cliffanet/sky-meter/cube/source/jump/proc.cpp

#include "proc.h"
#include "bmp280.h"
#include "altcalc.h"
#include "logbook.h"
#include "saver.h"
#include "bargraph.h"
#include "../sys/trwire.h"
#include "../sys/stm32drv.h"
#include "../sys/maincfg.h"
#include "../sys/power.h"
#include "../sys/err.h"
#include "../sys/log.h"
#include "../view/page.h"

#include <cmath>
#include "string.h"

#if HWVER < 2
static TransSPI _spi(GPIOB, GPIO_PIN_0);
#else
static TransSPI _spi(GPIOB, GPIO_PIN_10);
#endif
static BMP280 _bmp(_spi);
static float _press = 0, _temp = 0;

static AltCalc _ac;
static AltJmp _jmp(false);

#ifdef USE_JMPINFO
static AltSqBig _sq;
static AltStrict _jstr;
#endif // USE_JMPINFO

static LogBook::item_t _last = { 0 };

static uint8_t page = 0;

#ifdef USE_JMPTRACE
static jmp::log_ring_t _log;
static int _lmin = 0, _lmax = 0;
#endif // USE_JMPTRACE

    //-----------------------------------
    //---           draw
    //-----------------------------------

    static int16_t alt() {
        // Для отображения высоты app() лучше подходит,
        // т.к. она точнее показывает текущую высоту,
        // опаздывает от неё меньше, чем avg()
        int16_t alt = round(_ac.app().alt());
        int16_t o = alt % ALT_STEP;
        alt -= o;
        if (abs(o) > ALT_STEP_ROUND) alt+= o >= 0 ? ALT_STEP : -ALT_STEP;
        return alt;
    }

    static const char *strtm(char *s, uint32_t tm) {
        tm /= 1000;
        int sec = tm % 60;
        tm -= sec;

        if (tm <= 0) {
            sprn("%d s", sec);
            return s;
        }

        tm /= 60;
        int min = tm % 60;
        tm -= min;

        if (tm <= 0) {
            sprn("%d:%02d", min, sec);
            return s;
        }

        sprn("%ld:%02d:%02d", tm/60, min, sec);
        return s;
    }

    static const char *modestr(char *s, AltJmp::mode_t m) {
        const char *pstr =
            m == AltJmp::INIT       ? "INIT" :
            m == AltJmp::GROUND     ? "GND" :
            m == AltJmp::TAKEOFF    ? "TOFF" :
            m == AltJmp::FREEFALL   ? "FF" :
            m == AltJmp::CANOPY     ? "CNP" : "-";
        strcpy(s, pstr);
        return s;
    }

    //-----------------------------------
    static void _draw(DSPL_ARG) {
        Dspl::drawBatt(u8g2);
        Dspl::drawClock(u8g2);
        Dspl::drawServ(u8g2);
        
        char s[strsz], m[strsz], t[strsz];

        err::tostr(s, strsz);
        if (s[0] != '\0') {
            DSPL_FONT(u8g2_font_helvB08_tr);
            DSPL_STR(0, 17, s);
        }

    if (!_ac.isempty()) {
        // info
        DSPL_FONT(u8g2_font_6x13B_tr);

        uint8_t y = 40;
        sprn("%.1f m/s", _ac.avg().speed());
        DSPL_STR(static_cast<int>(DSPL_S_RIGHT(s))+60-DSPL_DWIDTH, y, s);

        y += DSPL_S_HEIGHT+2;
        sprn("%s (%s)", modestr(m, _jmp.mode()), strtm(t, _jmp.tm()));
        DSPL_STR(0, y, s);

#ifdef USE_JMPINFO
        y += DSPL_S_HEIGHT+2;
        if (_jmp.newtm() > 0) {
            sprn("new: %s (%ld)", strtm(t, _jmp.newtm()), _jmp.newcnt());
            DSPL_STR(0, y, s);
        }

        y += DSPL_S_HEIGHT+2;
        if (_jmp.ff().active()) {
            sprn("ff: %d", _jmp.ff().num());
            DSPL_STR(0, y, s);
        }

        y += DSPL_S_HEIGHT+2;
        sprn("q:%0.1f(%s)", _sq.val(), strtm(t, _sq.tm()));
        DSPL_STR(0, y, s);

        y += DSPL_S_HEIGHT+2;
        sprn("p[%0.0f]:%0.1f", _ac.pressgnd(), _press-_ac.pressgnd());
        DSPL_STR(0, y, s);

        //sprn("s[%d]:%s(%s)", _jstr.prof().num(), modestr(m, _jstr.mode()), strtm(t, _jstr.tm()));
        sprn("t:%.2f", _temp);
        DSPL_STR(DSPL_S_RIGHT(s)-15, DSPL_DHEIGHT-1, s);
#endif // USE_JMPINFO

    }

        // alt
        if (_ac.isempty())
            sprn("-");
        else
            sprn("%d", alt());
        
        switch (page) {
            case 0: {
                // alt
                DSPL_FONT(u8g2_font_logisoso62_tn);
                DSPL_STR(DSPL_S_RIGHT(s), 80, s);
            }
            break;
#ifdef USE_JMPTRACE
            case 1: {
                // alt
                DSPL_FONT(u8g2_font_fub20_tr);

                int y = DSPL_S_HEIGHT + 20;
                DSPL_STR(130-DSPL_S_WIDTH(s), y, s);

                // вертикальная шкала
                DSPL_LINE(DSPL_DWIDTH-5, 0,                 DSPL_DWIDTH, 0);
                DSPL_LINE(DSPL_DWIDTH-5, DSPL_DHEIGHT-1,    DSPL_DWIDTH, DSPL_DHEIGHT-1);
                DSPL_LINE(DSPL_DWIDTH-5, DSPL_DHEIGHT/2,    DSPL_DWIDTH, DSPL_DHEIGHT/2);

                DSPL_FONT(u8g2_font_blipfest_07_tn);
                sprn("%d", _lmin);
                DSPL_STR(DSPL_S_RIGHT(s)-6, DSPL_DHEIGHT-1, s);
                sprn("%d", _lmax);
                DSPL_STR(DSPL_S_RIGHT(s)-6, DSPL_S_HEIGHT, s);
                sprn("%d", _lmin+(_lmax-_lmin)/2);
                DSPL_STR(DSPL_S_RIGHT(s)-6, (DSPL_DHEIGHT+DSPL_S_HEIGHT-1)/2, s);

                // рисуем графики
#define LPADD 12
                double dx = static_cast<double>(DSPL_DWIDTH-LPADD) / _log.capacity();
                double xd = DSPL_DWIDTH;
                double dy = static_cast<double>(DSPL_DHEIGHT) / (_lmax-_lmin);
                for (const auto &l : _log) {
                    // точки графика
                    int x = static_cast<int>(round(xd));
                    int y = static_cast<int>(round(dy * (l.alt - _lmin)));
                    if ((y >= 0) && (y < DSPL_DHEIGHT)) {
                        y = DSPL_DHEIGHT-y-1;
                        DSPL_PIXEL(x, y);
                    
                        // высчитанное место изменения режима
                        if (l.mclc)
                            DSPL_DISC(x, y, 2);
                    }
                    
                    if (l.mchg)
                        // точка изменения режима (принятия реешения)
                        for (int y = 0; y < DSPL_DHEIGHT; y+=3)
                            DSPL_PIXEL(x, y);

                    xd -= dx;
                }
            }
            break;
#endif // USE_JMPTRACE
        }
    }
    //-----------------------------------

/* ------------------------------------------------------------------------------------------- *
 *  Текущее давление "у земли", нужно для отслеживания начала подъёма в режиме "сон"
 * ------------------------------------------------------------------------------------------- */
static AltSleep _slp;
    //-----------------------------------

namespace jmp {

    void init() {
        if (_bmp.init())
            CONSOLE("BMP280 ok: chipid=0x%02x, version=0x%02x", _bmp.chipid(), _bmp.version());
        else {
            err::add(0x50);
            CONSOLE("BMP280 fail (chipid: 0x%02x)", _bmp.chipid());
        }
        // тут мы оказываемся только после физической подачи питания,
        HAL_Delay(100); // надо дать успеть датчику проинициироваться
    }

    void setdraw() {
        Dspl::set(_draw);
    }

    void pagenxt() {
#ifdef USE_JMPTRACE
        page++; page %= 2;
#endif // USE_JMPTRACE
    }

    void resetgnd() {
        _ac.gndreset();
    }

    void resetmode() {
        _jmp.reset();
#ifdef USE_JMPINFO
        _sq.reset();
        _jstr.reset();
#endif // USE_JMPINFO
    }

    uint8_t chipid() {
        return _bmp.chipid();
    }

    float press() {
        return _press;
    }
    float temp() {
        return _temp;
    }

    AltJmp::mode_t mode() {
        return _jmp.mode();
    }

    bool isgnd() {
        return (_jmp.mode() == AltJmp::GROUND) && (_jmp.tm() > 60000);
    }

    const LogBook::item_t &last() {
        return _last;
    }

    const log_ring_t &trace() {
        return _log;
    }

    void sleep() {
        _slp.clear();
        _slp.tick(_ac.pressgnd());
        if (!_ac.isinit())
            _slp.tick(_ac.press());
        _ac.clear();
        _bmp.sleep();
        CONSOLE("saved");
    }

    bool sleep2toff(uint32_t ms) {
        if (!_bmp.setctrl()) {
            CONSOLE("NO BMP280");
            _slp.clear();
            err::add(0x54);
            return false;
        }
        
        float press;
        if (!_bmp.meas(press)) {
            CONSOLE("ERROR BMP280");
            _slp.clear();
            err::add(0x55);
            return false;
        }
        _slp.tick(press);
        bar::tick(press, ms);
        if (!_slp.istoff()) {
            _bmp.sleep();
            // Почему-то с первого раза не всегда уходит в сон.
            // Причём, перед повтором надо сделать паузу.
            HAL_Delay(1);
            _bmp.sleep();
            return false;
        }

        CONSOLE("TAKEOFF _pressgnd: %0.2f", _slp.pressgnd());
        _ac.gndset(_slp.pressgnd());
        _ac.tick(press, ms);
        _jmp.reset(AltJmp::TAKEOFF);
#ifdef USE_JMPINFO
        _sq.reset();
        _jstr.reset();
#endif // USE_JMPINFO
        _slp.clear();

        return true;
    }

    void sleep2gnd() {
        if (_slp.isempty())
            return;
        _ac.gndset(_slp.pressgnd());
        _slp.clear();
    }

    void tick(uint32_t ms) {
        if (!_bmp.meas(_press, _temp)) {
            err::add(0x55);
            return;
        }
        _ac.tick(_press, ms);

        static auto m = _jmp.mode();
        _jmp.tick(_ac);
        bar::tick(_jmp.mode() == AltJmp::GROUND ? _press : _ac.pressgnd(), ms);
        const bool chgmode = m != _jmp.mode();
#ifdef USE_JMPINFO
        _sq.tick(_ac);
        _jstr.tick(_ac);
#endif // USE_JMPINFO

        // gndreset
        if (
                (_jmp.mode() == AltJmp::GROUND) &&
                (abs(_ac.avg().speed()) < AC_SPEED_FLAT) &&
                (_jmp.tm() > ALT_AUTOGND_INTERVAL)
            ) {
            _ac.gndreset();
            _jmp.reset();
            CONSOLE("auto GND reseted");
        }

        // синий светодиод
        if (_jmp.mode() > AltJmp::TAKEOFF) {
            static uint8_t d = 0;
            d++;
            if (((_jmp.mode() == AltJmp::FREEFALL) && ((d % 2) == 0)) ||
                ((d % 8) == 0))
                HAL_GPIO_TogglePin(LED_PIN_BLUE);
        }
        else
        if (chgmode)
            HAL_GPIO_WritePin(LED_PIN_BLUE, _jmp.mode() > AltJmp::GROUND ? GPIO_PIN_SET : GPIO_PIN_RESET);

        // логбук
#ifdef USE_LOGBOOK
        if (chgmode)
            switch (_jmp.mode()) {
                case AltJmp::GROUND:
                    if (m > AltJmp::GROUND) {
                        _last = LogBook::end(_jmp.newtm());
                        jsave::full();
                    }
                    break;
                case AltJmp::TAKEOFF:
                    LogBook::beg_toff();
                    break;
                case AltJmp::FREEFALL:
#ifdef USE_JMPTRACE
                    LogBook::beg_ff(_jmp.newtm(), _log[_jmp.cnt()].alt);
#else // USE_JMPTRACE
                    LogBook::beg_ff(_jmp.newtm(), _ac.alt()+100);
#endif //USE_JMPTRACE
                    break;
                case AltJmp::CANOPY:
#ifdef USE_JMPTRACE
                    LogBook::beg_cnp(_jmp.newtm(), _log[_jmp.cnt()].alt);
#else // USE_JMPTRACE
                    LogBook::beg_cnp(_jmp.newtm(), _ac.alt()+100);
#endif //USE_JMPTRACE
                    break;
                default:
                    break;
            }
        
        switch (_jmp.mode()) {
            case AltJmp::TAKEOFF:
                LogBook::tick_toff(ms);
                break;
            case AltJmp::FREEFALL:
                LogBook::tick_ff(ms);
                break;
            case AltJmp::CANOPY:
                LogBook::tick_cnp(ms);
                break;
            default:
                break;
        }

#else // USE_LOGBOOK

        if ((m > AltJmp::GROUND) && (_jmp.mode() == AltJmp::GROUND)) {
            // При отсутствии LogBook
            // будем сами увеличивать кол-во прыжков
            (*cfg)->jmpcnt ++;
            cfg.save();
            jsave::full();
        }

#endif // USE_LOGBOOK




#ifdef USE_JMPTRACE
        // добавление в _log
        char mchg =
            !chgmode                        ? 0 :
            _jmp.mode() == AltJmp::INIT     ? 'i' :
            _jmp.mode() == AltJmp::GROUND   ? 'g' :
            _jmp.mode() == AltJmp::TAKEOFF  ? 't' :
            _jmp.mode() == AltJmp::FREEFALL ? 'f' :
            _jmp.mode() == AltJmp::CANOPY   ? 'c' : '-';
        _log.push({ static_cast<int>(_ac.buf().alt()), 0, mchg });
        if (chgmode && (_jmp.cnt() < _log.size()))
            _log[_jmp.cnt()].mclc = mchg;

        _lmin = _log[0].alt;
        _lmax = _log[0].alt;
        for (const auto &l : _log) {
            if (_lmin > l.alt)
                _lmin = l.alt;
            if (_lmax < l.alt)
                _lmax = l.alt;
        }

        auto y = _lmin - (_lmin % 300);
        if (y > _lmin+5) y -= 300; // +5, чтобы случайные -1-2m не уводили в -300
        _lmin = y;
        for (; y <= 15000; y += 300)
            if (y > _lmax) break;
        _lmax = y;
        // -------------------
#endif // USE_JMPTRACE

        if (chgmode) {
            m = _jmp.mode();
            _jmp.resetnew();
        }
    }

} // namespace jmp 
