cliffanet/sky-meter/cube/source/sdcard/fshnd.h

#ifndef _sdcard_fshnd_H
#define _sdcard_fshnd_H

#include "../ff/ff.h"
#include "../def.h"

//#define FR(func, fail)      { CONSOLE(TOSTRING(func)); auto st = func; if (st != FR_OK) { CONSOLE(TOSTRING(func) "failed: %d", st); fail; } }
#define FR(func, fail)      { auto st = func; if (st != FR_OK) { CONSOLE(TOSTRING(func) "failed: %d", st); fail; } }
#define F(func)            FR(func, ;)

namespace fs {
    bool mount();
    bool stop();
    bool ismount();

    class mounter {
        bool _ok;
    public:
        mounter() { _ok = mount(); }
        ~mounter(){ if (_ok) stop(); }
        operator bool() const { return _ok; }
    };

    const FATFS & inf();

    typedef enum {
        CT_UNKNOWN  = -1,
        CT_NONE     = 0,
        CT_MMC3     = 0x01,		/* MMC ver 3 */
        CT_MMC4     = 0x02,		/* MMC ver 4+ */
        CT_MMC      = 0x03,		/* MMC */
        CT_SDC1     = 0x04,		/* SD ver 1 */
        CT_SDC2     = 0x08,		/* SD ver 2+ */
        CT_SDC      = 0x0C,		/* SD */
        CT_BLOCK    = 0x10,		/* Block addressing */
        CT_SDC2BL   = 0x10|0x08 /* SD ver 2+, Block addressing */
    } ctype_t;

    ctype_t ctype();

    class File {
        FIL _fh = { 0 };
        bool _ok;
    
        public:
            File();
            File(const TCHAR *path, BYTE mode = FA_READ);
            ~File();
            bool open(const TCHAR *path, BYTE mode = FA_READ);
            bool close();
            operator bool() const { return _ok; };
            FIL * operator&() { return &_fh; }
            const FIL * operator->() const { return &_fh; }
            int32_t read(void *buff, UINT btw);
            bool write(const void *buff, UINT btw);
    };

#ifdef FWVER_DEBUG
    bool test();
#endif // FWVER_DEBUG
}

#endif // _sdcard_fshnd_H
