cliffanet/sky-meter/cube/source/view/text.en.h

/*
    View: Text lang
*/

#ifndef _view_text_lang_H
#define _view_text_lang_H

#define menuFont        u8g2_font_ncenB08_tr

#define TXT_MENU_EXIT               "> exit"
#define TXT_MENU_CONFIRM            "confirm?"
#define TXT_MENU_ON                 "On"
#define TXT_MENU_OFF                "Off"
#define TXT_MENU_YES                "Yes"
#define TXT_MENU_NO                 "No"
#define TXT_MENU_OK                 "OK"
#define TXT_MENU_FAIL               "fail"

#define TXT_MAIN_JMPCNT             "Jump count"
#define TXT_MAIN_LOGBOOK            "LogBook"
#define TXT_MAIN_FLIP180            "Flipped 180"
#define TXT_MAIN_CONTRAST           "Contrast"
#define TXT_MAIN_ALT                "Altimeter"
#define TXT_MAIN_BARGRAPH           "Barometer"
#define TXT_MAIN_SYSTEM             "System"

#define TXT_ALT_AUTOGND             "Auto correct GND"
#define TXT_ALT_METER               "Alt (<1000) on meter"
#define TXT_ALT_CORRECT             "Alt correction"
#define TXT_ALT_RESETGND            "Reset GND now"
#define TXT_ALT_RESETMODE           "Reset mode"
#define TXT_ALT_SAVETRACE           "Save trace"

#define TXT_SYSTEM_DATETIME         "Change Clock"
#define TXT_SYSTEM_LOPWRONJMP       "LoPwr on jump"
#define TXT_SYSTEM_RESET            "Reset CPU"
#define TXT_SYSTEM_POWEROFF         "Power OFF"
#define TXT_SYSTEM_CFGDEFAULT       "Factory default"
#define TXT_SYSTEM_HWTEST           "Hardware test"

#define TXT_TEST_SERIAL             "s/n"
#define TXT_TEST_FLASHSZ            "Flash size"
#define TXT_TEST_FWVER              "FW ver"
#define TXT_TEST_CLOCK              "Clock"
#define TXT_TEST_BATTERY            "Battery"
#define TXT_TEST_BATTCHARGE         "Batt charge"
#define TXT_TEST_PRESSID            "Press ID"
#define TXT_TEST_PRESSURE           "Pressure"
#define TXT_TEST_PTEMP              "Temp"
#define TXT_TEST_PTEMPVAL           "%0.1f"
#define TXT_TEST_PRESSVAL           "(%0.0f Pa) %s"
#define TXT_TEST_LIGHT              "Light test"
#define TXT_TEST_SDCARD             "SD-card"

#define TXT_LOGBOOK_JUMPNUM         "Jump # %ld"
#define TXT_LOGBOOK_ALTEXIT         "Alt"
#define TXT_LOGBOOK_ALTCNP          "Deploy"
#define TXT_LOGBOOK_TIMETOFF        "Takeoff"
#define TXT_LOGBOOK_TIMEFF          "FF time"
#define TXT_LOGBOOK_TIMESEC         "%d s"
#define TXT_LOGBOOK_MINSEC          "%d:%02d"
#define TXT_LOGBOOK_TIMECNP         "CNP time"
#define TXT_LOGBOOK_TRACE           "Trace"

#endif // _view_text_lang_H
