cliffanet/sky-meter/cube/source/view/page.h

/*
    Display: page frames
*/

#ifndef _view_page_H
#define _view_page_H

#include "dspl.h"

namespace Dspl {

    void drawBatt(DSPL_ARG);
    void drawClock(DSPL_ARG);
    void drawServ(DSPL_ARG);

    void page();

}; // namespace Dspl

#endif // _view_page_H
